klym-tatarnikov/RoboDesk/firmware/src/LogicData.cpp

#include "Arduino.h"
#include "LogicData.h"

// Copyright (c) 2017 Phil Hord
// MIT License

// Expect 1 bit per millisecond
#define SAMPLE_RATE 1000

// Push to head; pop from tail

index_t mque::next(index_t x)
{
  return ( x + 1 ) % Q_MAX;
}

bool mque::empty() {
  return tail == head;
}

bool mque::full() {
  return next(tail) == head;
}

index_t mque::size()
{
  return (Q_MAX + head - tail) % Q_MAX;
}

// destructive push; pushes even if full
void mque::push(micros_t t)
{
  // NOTE: Caller should have disabled interrupts
  trace[head] = t;
  head = next(head);
  if (tail == head) {
    tail = next(tail);
  }
}

// destructive pop; no-op if empty
bool mque::pop(micros_t * t)
{
  lock _;
  if (empty()) return false;
  *t = trace[tail];
  tail = next(tail);
  return true;
}

// drop elements from the tail of the queue; no range-checking!
void mque::drop(index_t n)
{
  lock _;
  tail += n;
  tail %= Q_MAX;  // TODO: Check if this is expensive
}

// non-destructive indexed peek
bool mque::peek(index_t index, micros_t * t)
{
  lock _;
  if (index >= size()) return false;
  index += tail;
  index %= Q_MAX;
  *t = trace[index];
  return true;
}

//------------------------------------------------------

void LogicData::Begin() {
  if(tx_pin != NULL) {
    pinMode(tx_pin, OUTPUT);
    SendBit(MARK); // IDLE-CLOSED
  }
}

void LogicData::PinChange(bool level) {
  // Assumes interrupts disabled
  // Expect HIGH level on even queue steps
  bool sync = q.head & 1;
  if (level == sync) {
    micros_t now = micros();
    if (pin_idle) {
      q.push(BIG_IDLE);
      pin_idle = false;
    } else {
      q.push(now-prev_bit);
    }
    prev_bit = now;
  }
}

void LogicData::Service() {
  micros_t idle_time = micros() - prev_bit;
  if (!pin_idle && idle_time >= IDLE_TIME) {
    lock _;
    if (micros() - prev_bit >= IDLE_TIME) {
      pin_idle = true;
    }
  }
}

// Calculate parity and set in lsb of message
uint32_t LogicData::Parity(uint32_t msg) {
  unsigned par_count = 0;
  for (uint32_t mask = 2; mask ; mask <<= 2) {
      par_count += msg & mask;
  }
  msg |= par_count & 1;
  return msg;
}

bool LogicData::CheckParity(uint32_t msg) {
  return Parity(msg) == msg;
}

//void LogicData::DumpQueue() {
//  lock _;
//  fini=q.tail;
//  bool level = ((q.size() & 1)==0) ^ !prev_level;
//}

uint32_t LogicData::ReadTrace() {
  index_t fini;

  {
    lock _;
    fini=q.tail;
  }

  bool level = !(fini & 1);
  micros_t t;
  index_t i=0;

  //-- Find start-bit (idle-low followed by high-pulse shorter than 2-bits)
  for (; q.peek(i, &t); i++) {
    if (!level && t > static_cast<micros_t>(40) * SAMPLE_RATE) {
      micros_t t1;
      if (q.peek(i+1, &t1) && t1 < SAMPLE_RATE*2)  break;
    }
    level = !level;
  }

  //-- Sample signals at mid-point of data rate
  uint32_t mask = 1ULL<<31;
  uint32_t acc = 0;
  acc = 0;
  micros_t t_meas = SAMPLE_RATE/2;
  for (t=0; mask; mask >>= 1) {
    if (t_meas < SAMPLE_RATE) {
      if (!q.peek(++i, &t)) break;
      level = !level;
      t_meas += t;
    }
    acc += !level ? mask : 0;
    t_meas -= SAMPLE_RATE;
  }

  // ran out of signal before we got whole word
  if (mask) return 0;

  // We decoded a word and it consumed i samples
  lock _;
  if (fini == q.tail) {
    q.drop(i-1);
  } else {
    // race fail; return 0 and let the caller try again later
    acc = 0;
  }

  return acc;
}

bool LogicData::IsValid(uint32_t msg) {
  if ((msg & 0xFFF00000) != 0x40600000) {
    return false;
  }
  return CheckParity(msg);
}

bool LogicData::IsNumber(uint32_t msg) {
  return IsValid(msg) && (msg & 0xFFE00) == 0x00400;
}

const char * LogicData::MsgType(uint32_t msg) {
  if ((msg & 0xFFF00000) != 0x40600000) {
    return "INVAL";
  }

  if (!CheckParity(msg)) {
    return "PARIT";
  }

  // Display number
  if ((msg & 0xFFE00) == 0x00400) {
    return "NUMBR";
  }

  // Display command
  if ((msg & 0xFFFF) == 0x1400) {
    return "DISPL";
  }

  return "UKNWN";
}

static uint8_t ReverseNibble(uint8_t in) {
  uint8_t ret = 0;
  ret |= (in << 3) & 8;
  ret |= (in << 1) & 4;
  ret |= (in >> 1) & 2;
  ret |= (in >> 3) & 1;
  return ret;
}

static uint8_t ReverseByte(uint8_t in) {
  return (ReverseNibble(in) << 4) + ReverseNibble(in>>4);
}

static uint16_t ReverseWord(uint16_t in) {
  return (ReverseByte(in) << 8) + ReverseByte(in>>8);
}

uint8_t LogicData::GetNumber(uint32_t msg) {
  if (IsNumber(msg)) {
    return ReverseByte(msg>>1);
  }
  return 0;
}

const char * LogicData::Decode(uint32_t msg) {
  static char buf[20];

  // 0x40600400
  // 0x20300200
  //         ^^ display byte
  //      ^^^    command
  uint16_t w = ReverseWord(msg>>9)>>4;
  uint8_t  b = ReverseByte(msg>>1);

  if ((msg & 0xFFF00000) != 0x40600000) {
    sprintf(buf, "%08lx ??", msg);
  } else if (!CheckParity(msg)) {
    sprintf(buf, "%08lx !", msg);
  } else if (w == 0x400) {
    // Display number
      sprintf(buf, "%03u", b);
  } else if (msg == 0x40611400) {
      sprintf(buf, "Display ON");
  } else if (msg == 0x406e1400) {
      sprintf(buf, "Display OFF");
  } else {
    sprintf(buf, "%08lx  %03x %02x", msg, w, b);
  }

  return buf;
}

// Transmit
void LogicData::SendBit(bool bit) {
  if(tx_pin != NULL) {
    digitalWrite(tx_pin, bit);
  }
}

void LogicData::MicroDelay(micros_t us) {
  // spin-wait until timer advances
  while (true) {
    Service();
    micros_t now = micros();
    now -= timer;
    if (now >= us) break;
    // TODO: if (t-now > 50) usleep(t-now-50);
  }
  timer += us;
}

void LogicData::Delay(uint16_t ms) {
  MicroDelay(micros_t(ms)*1000);
}

void LogicData::SendBit(bool bit, uint16_t ms) {
  SendBit(bit);
  Delay(ms);
}

void LogicData::Space(uint16_t ms) {
  SendBit(SPACE, ms);
}

void LogicData::SendStartBit() {
  Space(LOGICDATA_MIN_START_BIT);
}

void LogicData::LogicData::Stop() {
  SendBit(MARK); // IDLE-CLOSED
}

void LogicData::Send(uint32_t data) {
  SendStartBit();

  for (uint32_t i = 0x80000000 ; i; i/=2) {
    SendBit((i&data)?SPACE:MARK, 1);
  }

  SendBit(SPACE); // IDLE-OPEN
}

void LogicData::OpenChannel() {
  if (active) return;
  active = true;
  start = timer = micros();
  SendBit(SPACE);
}

void LogicData::CloseChannel() {
  // Send a SPACE at least long enough so our command-channel was open for 500ms, or
  // just start-bit length if we've already been open that long.

  if (!active) return;


  // Workaround for stuck timers
  Stop();
  return;

  // BUG: Following timers never expire!
  micros_t delta = timer-start;
  if (delta/1000 + LOGICDATA_MIN_START_BIT < LOGICDATA_MIN_WINDOW_MS) {
    timer=start;
    Space(LOGICDATA_MIN_WINDOW_MS);
  } else {
    Space(LOGICDATA_MIN_START_BIT);
  }
  Stop();

  active = false;
}

void LogicData::Send(uint32_t * data, unsigned count) {
  if (!count) return;

  OpenChannel();
  for (unsigned i = 0; i != count; i++) {
    Send(data[i]);
  }
  CloseChannel();
}

//
// LOGICDATA protocol
//////////////////////////////////////////////////////////
