klym-tatarnikov/RoboDesk/firmware/src/CREDENTIALS.h

const char* WIFI_SSID = "";
const char* WIFI_PASS = "";
const char* mqtt_server = "192.168.1.1";

IPAddress ip(192, 168, 1, 222);
IPAddress gateway(192, 168, 1, 1);
IPAddress subnet(255, 255, 255, 0);
IPAddress dns(192, 168, 1, 1);
